A-Bade/28Pin-Arduino-Uno-PCB-Board/!Design Documentation/3D models/m20-7821046_asm.stp

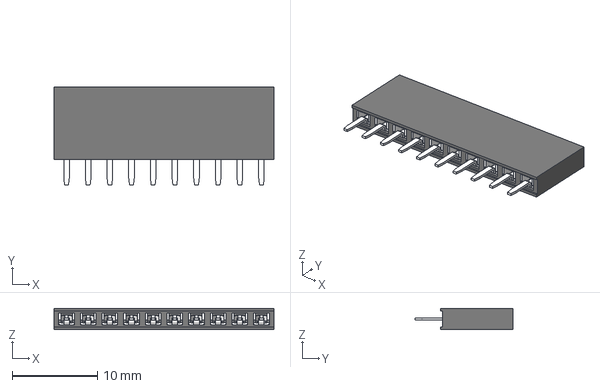
[picture p16: CAD file, 2025-02-28]
!Design Documentation/3D models/m20-7821046_asm.stp
25.8 x 11.5 x 2.50 mm
M20-78210_MOULD
M20-782_CONTACT x 10
