A-Bade/28Pin-Arduino-Uno-PCB-Board/!Design Documentation/3D models/m20-7820842_asm.stp

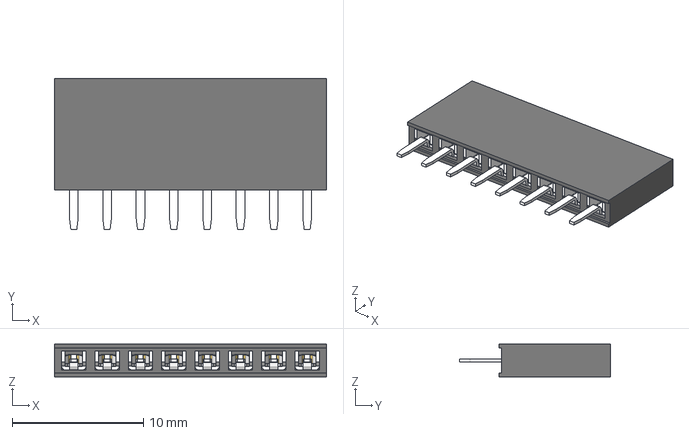
[picture p17: CAD file, 2025-02-28]
!Design Documentation/3D models/m20-7820842_asm.stp
20.7 x 11.5 x 2.50 mm
M20-78208_MOULD
M20-782_CONTACT x 8
