A-Bade/28Pin-Arduino-Uno-PCB-Board/!Design Documentation/3D models/m20-7820646_asm.stp

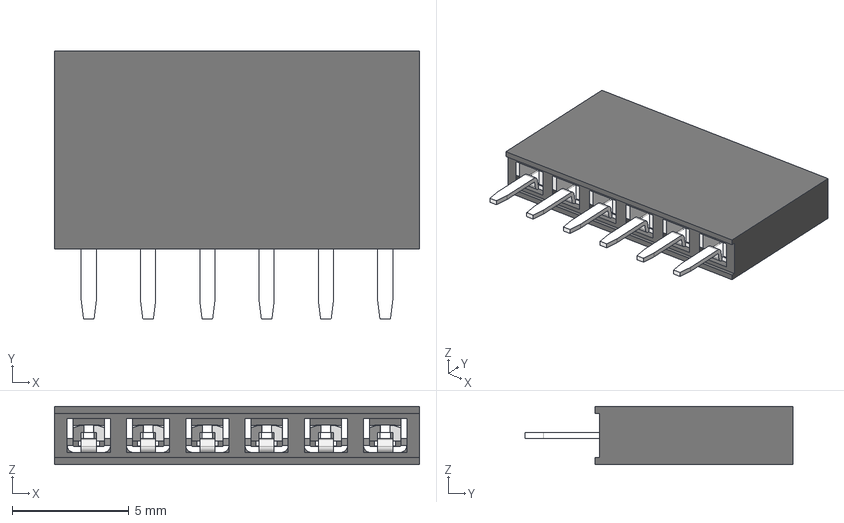
[picture p18: CAD file, 2025-02-28]
!Design Documentation/3D models/m20-7820646_asm.stp
15.6 x 11.5 x 2.50 mm
M20-78206_MOULD
M20-782_CONTACT x 6
