A-Bade/28Pin-Arduino-Uno-PCB-Board/!Design Documentation/Templates/!Released Files/Step 5 - Schematic/read_me.txt

Update Schematic Cover Page to RELEASED DD-MMM-YYYY
Place here PDF version of schematic, if possible one for each BOM variant.
