A-Bade/28Pin-Arduino-Uno-PCB-Board/!Design Documentation/Templates/!Released Files/Step 1 - PCB Manufacturing/NC Drill Output/read_me.txt

Place here drill files and documents which explain it (e.g. for HDI PCB you can put here pdf showing drills for each layer pair)
